kosomoN/elepaja19/control_mc/avr-i2c/i2c.c

/*
 * The MIT License (MIT)
 *
 * Copyright (c) 2014 Pieter Noordhuis
 *
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
 * THE SOFTWARE IS PROVIDED "AS IS", WITHOUT WARRANTY OF ANY KIND, EXPRESS OR
 * IMPLIED, INCLUDING BUT NOT LIMITED TO THE WARRANTIES OF MERCHANTABILITY,
 * FITNESS FOR A PARTICULAR PURPOSE AND NONINFRINGEMENT. IN NO EVENT SHALL THE
 * AUTHORS OR COPYRIGHT HOLDERS BE LIABLE FOR ANY CLAIM, DAMAGES OR OTHER
 * LIABILITY, WHETHER IN AN ACTION OF CONTRACT, TORT OR OTHERWISE, ARISING FROM,
 * OUT OF OR IN CONNECTION WITH THE SOFTWARE OR THE USE OR OTHER DEALINGS IN THE
 * SOFTWARE.
 */

#include <assert.h>
#include <avr/interrupt.h>
#include <avr/io.h>
#include <stdio.h>
#include <stdlib.h>

#include "i2c.h"

/* Pointers to current txn and op. */
static volatile i2c_txn_t *txn;
static volatile i2c_op_t *op;

/*
 * By default, the control register is set to:
 *  - TWEA: Automatically send acknowledge bit in receive mode.
 *  - TWEN: Enable the I2C system.
 *  - TWIE: Enable interrupt requests when TWINT is set.
 */
#define TWCR1_DEFAULT (_BV(TWEA) | _BV(TWEN) | _BV(TWIE))

#define TWCR1_NOT_ACK (_BV(TWINT) | _BV(TWEN) | _BV(TWIE))
#define TWCR1_ACK (TWCR1_NOT_ACK | _BV(TWEA))

void i2c_init(void) {
  uint8_t sreg;

  /* Store the status register and disable interrupts. */
  sreg = SREG;
  cli();

  /*
   * From ATmega328P datasheet:
   *   SCL freq = (CPU Clock freq) / (16 + 2(TWBR1) * (PrescalerValue))
   *
   * Which means:
   *   TWBR1 = ((CPU Clock freq) / (SCL freq) - 16) / (2 * (PrescalerValue))
   *
   * Disable the prescaler and set TWBR1 according to CPU freq and SCL freq.
   */
  TWSR1 &= ~(_BV(TWPS1) | _BV(TWPS0));
  TWBR1 = ((F_CPU / I2C_FREQ) - 16) / (2 * 1);

  /* Enable interrupts via the control register. */
  TWCR1 = TWCR1_DEFAULT;

  /* Disable slave mode. */
  TWAR1 = 0;

  /* Restore the status register. */
  SREG = sreg;
}

void i2c_post(i2c_txn_t *t) {
  uint8_t sreg;

  /* Reset transaction attributes. */
  t->flags = 0;
  t->opspos = 0;
  t->next = NULL;

  sreg = SREG;
  cli();

  /* Append transaction to linked list. */
  if (txn == NULL) {
    txn = t;
    op = &txn->ops[0];

    /* Transmit START to kickstart things. */
    TWCR1 = 0;
    TWCR1 = TWCR1_DEFAULT | _BV(TWINT) | _BV(TWSTA);
  } else {
    volatile i2c_txn_t *txn_ = txn;
    while (txn_ != NULL) {
      if (txn_->next != NULL) {
        txn_ = txn_->next;
      } else {
        txn_->next = t;
        break;
      }
    }
  }

  SREG = sreg;
}

ISR(TWI1_vect, ISR_BLOCK) {
  uint8_t status = TWSR1 & TW_STATUS_MASK;

  /* This interrupt should only fire if there is something to do. */
  assert(op != NULL);
  if ((op->address & _BV(0)) == TW_READ) {
    /* Master Receiver mode. */
    switch (status) {

    /* A START condition has been transmitted. */
    case TW_START:
    /* A repeated START condition has been transmitted. */
    case TW_REP_START:
      assert(op->buflen > 0);
      op->bufpos = 0;
      TWDR1 = op->address;
      TWCR1 = TWCR1_DEFAULT | _BV(TWINT);
      break;

    /* Arbitration lost in SLA+R or NOT ACK bit. */
    case TW_MR_ARB_LOST:
      /* A START condition will be transmitted when the bus becomes free. */
      TWCR1 = TWCR1_DEFAULT | _BV(TWINT) | _BV(TWSTA);
      break;

    /* SLA+R has been transmitted; ACK has been received. */
    case TW_MR_SLA_ACK:
      if (op->buflen == 1) {
        TWCR1 = TWCR1_NOT_ACK;
      } else {
        TWCR1 = TWCR1_ACK;
      }
      break;

    /* SLA+R has been transmitted; NOT ACK has been received. */
    case TW_MR_SLA_NACK:
      txn->flags = I2C_TXN_DONE | I2C_TXN_ERR;
      goto next_txn;

    /* Data byte has been received; ACK has been returned. */
    case TW_MR_DATA_ACK:
      op->buf[op->bufpos++] = TWDR1;
      if (op->bufpos+1 == op->buflen) {
        TWCR1 = TWCR1_NOT_ACK;
      } else {
        TWCR1 = TWCR1_ACK;
      }
      break;

    /* Data byte has been received; NOT ACK has been returned. */
    case TW_MR_DATA_NACK:
      op->buf[op->bufpos++] = TWDR1;
      goto next_op;

    default:
      assert(0 && "unknown status in master receiver mode");
    }
  } else {
    /* Master Transmitter mode. */
    switch (status) {

    /* A START condition has been transmitted. */
    case TW_START:
    /* A repeated START condition has been transmitted. */
    case TW_REP_START:
      assert(op->buflen > 0);
      op->bufpos = 0;
      TWDR1 = op->address;
      TWCR1 = TWCR1_DEFAULT | _BV(TWINT);
      break;

    /* Arbitration lost in SLA+W or data bytes. */
    case TW_MT_ARB_LOST:
      /* A START condition will be transmitted when the bus becomes free. */
      TWCR1 = TWCR1_DEFAULT | _BV(TWINT) | _BV(TWSTA);
      break;

    /* SLA+W has been transmitted; ACK has been received. */
    case TW_MT_SLA_ACK:
      TWDR1 = op->buf[op->bufpos++];
      TWCR1 = TWCR1_DEFAULT | _BV(TWINT);
      break;

    /* SLA+W has been transmitted; NOT ACK has been received. */
    case TW_MT_SLA_NACK:
      txn->flags = I2C_TXN_DONE | I2C_TXN_ERR;
      goto next_txn;

    /* Data byte has been transmitted; ACK has been received. */
    case TW_MT_DATA_ACK:
      if (op->bufpos < op->buflen) {
        TWDR1 = op->buf[op->bufpos++];
        TWCR1 = TWCR1_DEFAULT | _BV(TWINT);
        break;
      }

      /* No more bytes left to transmit... */
      goto next_op;

    /* Data byte has been transmitted; NOT ACK has been received. */
    case TW_MT_DATA_NACK:
      if (op->bufpos < op->buflen) {
        /* There were more bytes left to transmit! */
        txn->flags = I2C_TXN_DONE | I2C_TXN_ERR;
        goto next_txn;
      }

      goto next_op;

    default:
      assert(0 && "unknown status in master transmitter mode");
    }
  }

  return;

next_op:
  /*
   * Advance to next operation in transaction, if possible.
   */
  if (++(txn->opspos) < txn->opslen) {
    op = &txn->ops[txn->opspos];

    /* Repeated start. */
    TWCR1 = TWCR1_DEFAULT | _BV(TWINT) | _BV(TWSTA);
    return;
  }

  /* No more operations, mark transaction as done. */
  txn->flags = I2C_TXN_DONE;

next_txn:
  /*
   * Advance to next transaction, if possible.
   */
  if (txn->next != NULL) {
    txn = txn->next;
    op = &txn->ops[0];

    /* Repeated start. */
    TWCR1 = TWCR1_DEFAULT | _BV(TWINT) | _BV(TWSTA);
    return;
  }

  txn = NULL;
  op = NULL;

  /* No more transaction, transmit STOP. */
  TWCR1 = TWCR1_DEFAULT | _BV(TWINT) | _BV(TWSTO);
}
