kosomoN/elepaja19/ui/constants.h

#ifndef CONSTANTS_H_
#define CONSTANTS_H_

#define MISO_PIN    9
#define RESET_A_PIN 5
#define RESET_B_PIN 25
#define RELAY_A_PIN 23
#define RELAY_B_PIN 24

#define MAX_CURRENT_A 3.0
#define MAX_VOLTAGE_V 24.0

#endif
