kosomoN/elepaja19/ui/keymap.h

#ifndef KEYMAP_H_
#define KEYMAP_H_

#define UIK_A_SELECT        KEY_A
#define UIK_B_SELECT        KEY_B
#define UIK_A_TOGGLE        KEY_G
#define UIK_B_TOGGLE        KEY_H

#define UIK_ENCODER_PRESS   KEY_C
#define UIK_ENCODER_CW      KEY_UP
#define UIK_ENCODER_CCW     KEY_DOWN

#define UIK_0               KEY_ZERO
#define UIK_1               KEY_ONE
#define UIK_2               KEY_TWO
#define UIK_3               KEY_THREE
#define UIK_4               KEY_FOUR
#define UIK_5               KEY_FIVE
#define UIK_6               KEY_SIX
#define UIK_7               KEY_SEVEN
#define UIK_8               KEY_EIGHT
#define UIK_9               KEY_NINE
#define UIK_DOT             KEY_PERIOD

#define UIK_VOLT            KEY_I
#define UIK_MVOLT           KEY_J
#define UIK_AMP             KEY_K
#define UIK_MAMP            KEY_L

#define UIK_UI0             KEY_D
#define UIK_UI1             KEY_E
#define UIK_UI2             KEY_F

#endif
